ucsb-biomimetic/ising-potts-with-SPADs-discrete/VRSPAD-144/code_and_data/results/coloring_ising_parameter_sweep.png

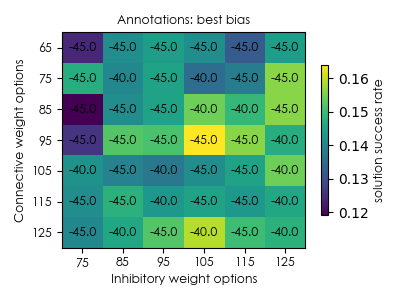
VRSPAD-144/code_and_data/results/coloring_ising_parameter_sweep.png
