ucsb-biomimetic/ising-potts-with-SPADs-discrete/VRSPAD-144/code_and_data/results/coloring_soln_vis.png

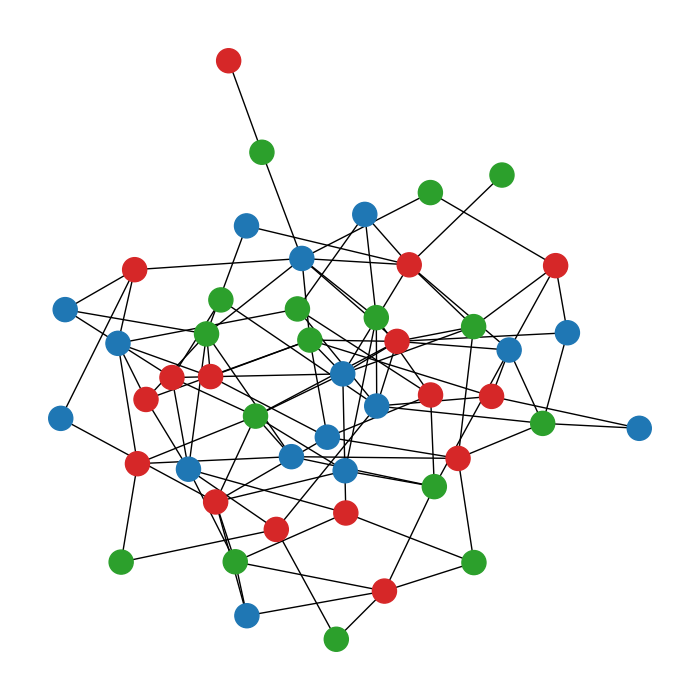
VRSPAD-144/code_and_data/results/coloring_soln_vis.png
