ucsb-biomimetic/ising-potts-with-SPADs-discrete/VRSPAD-144/code_and_data/results/tsp_annealing.png

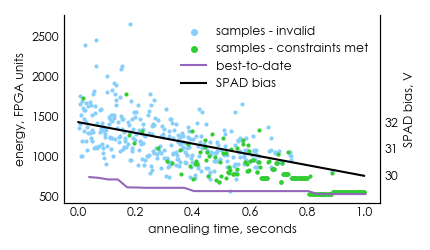
VRSPAD-144/code_and_data/results/tsp_annealing.png
