ucsb-biomimetic/ising-potts-with-SPADs-discrete/VRSPAD-144/pcb_design/VRSPAD-144.kicad_sch

## KiCad design VRSPAD-144/pcb_design/VRSPAD-144.kicad_sch (2023-06-14)

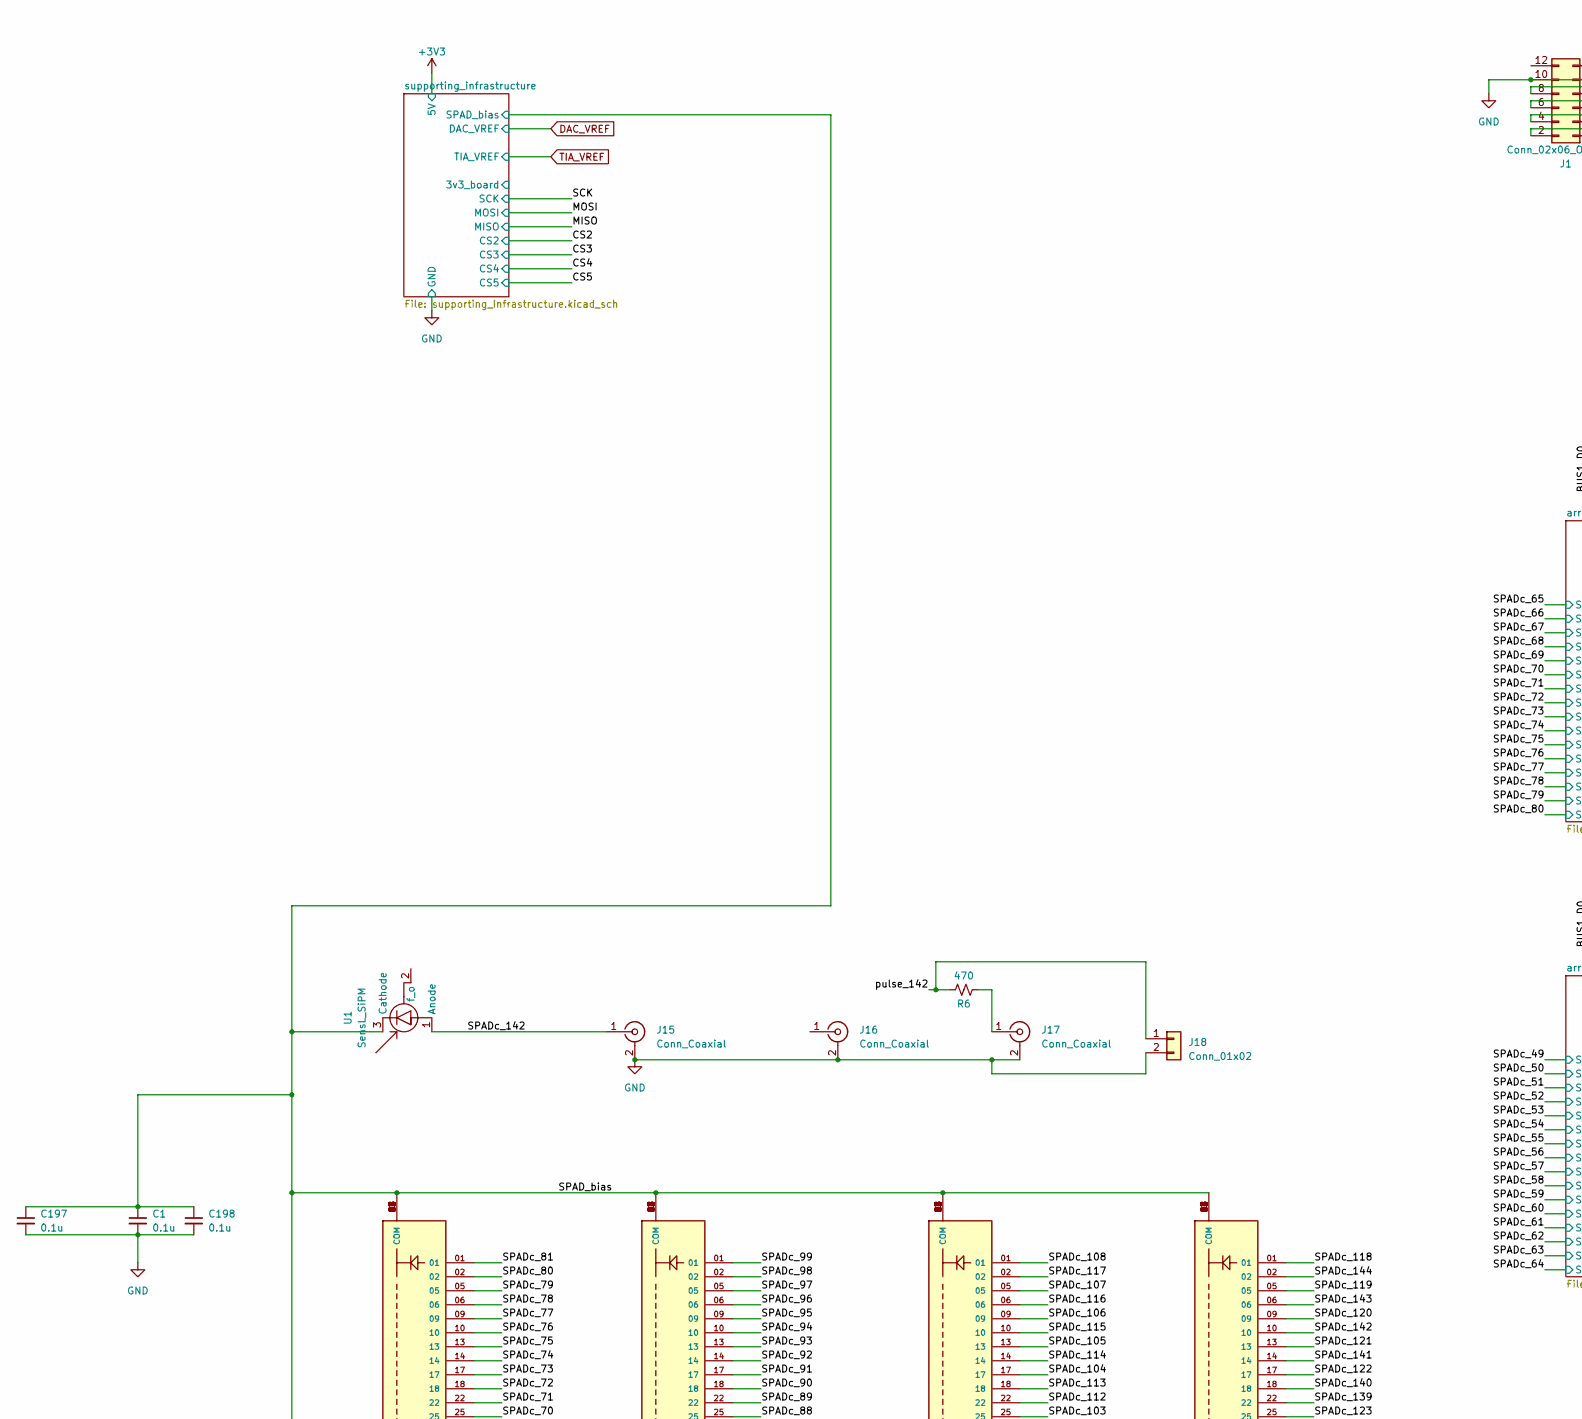
[picture p27: schematic VRSPAD-144.kicad_sch, part in row 1, column 1]

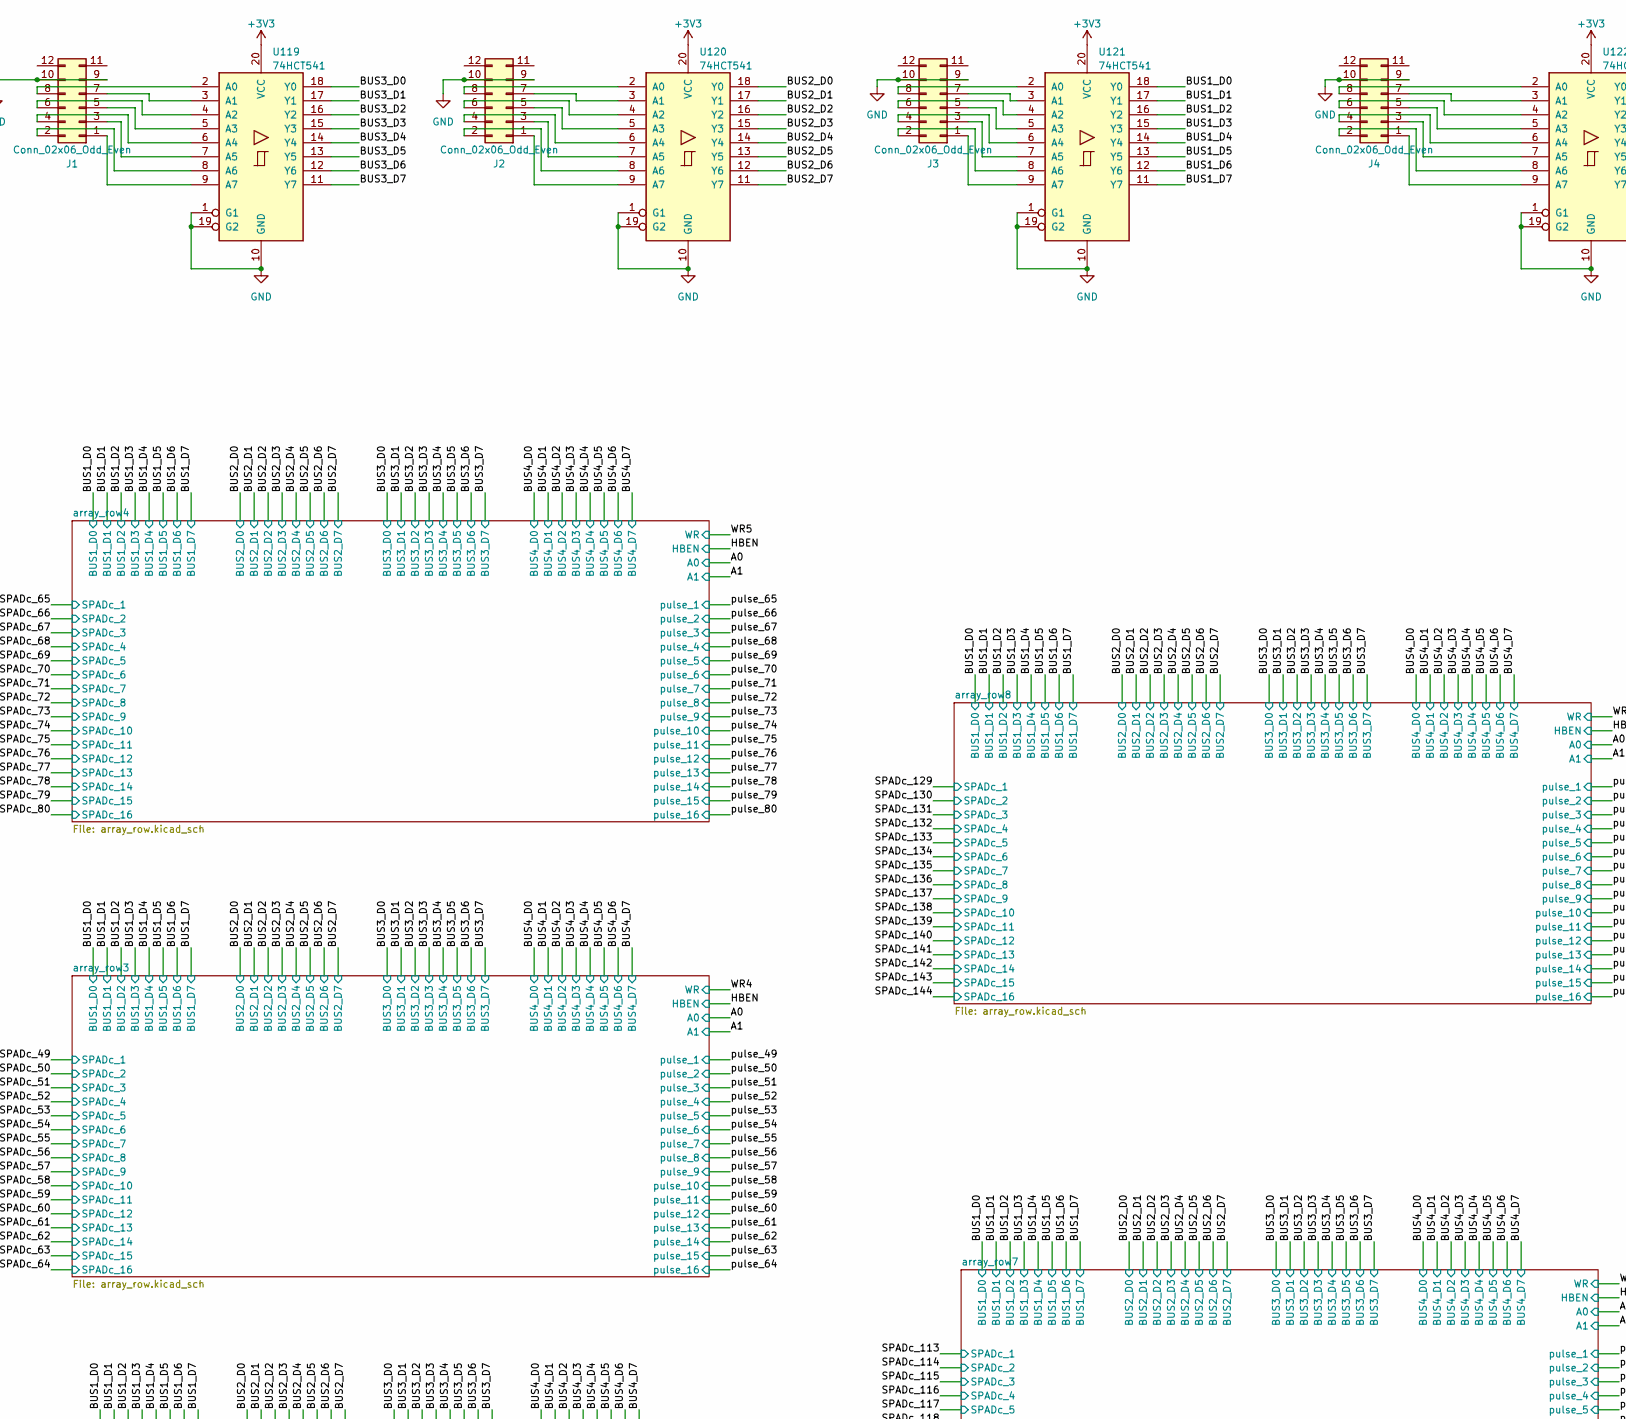
[picture p28: schematic VRSPAD-144.kicad_sch, part in row 1, column 2]

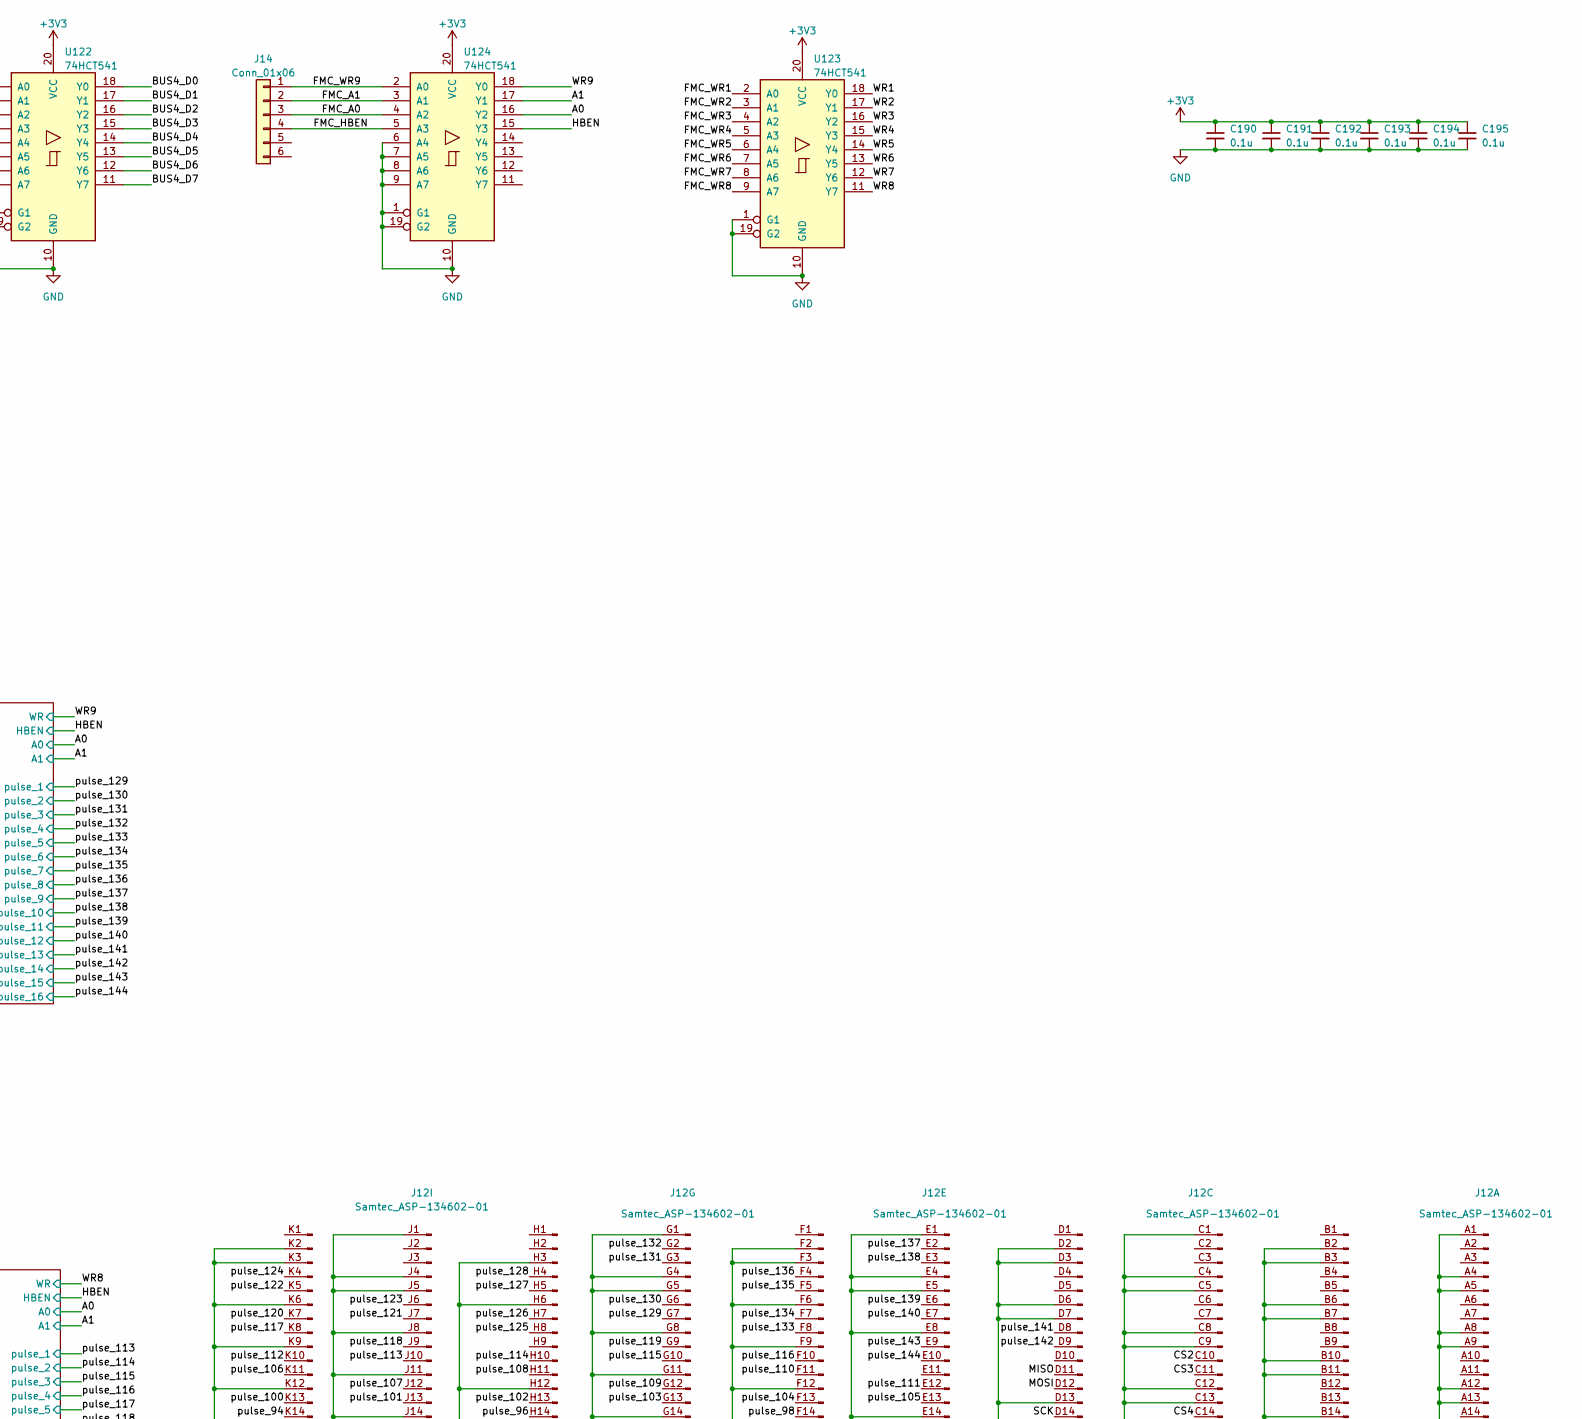
[picture p29: schematic VRSPAD-144.kicad_sch, part in row 1, column 3]

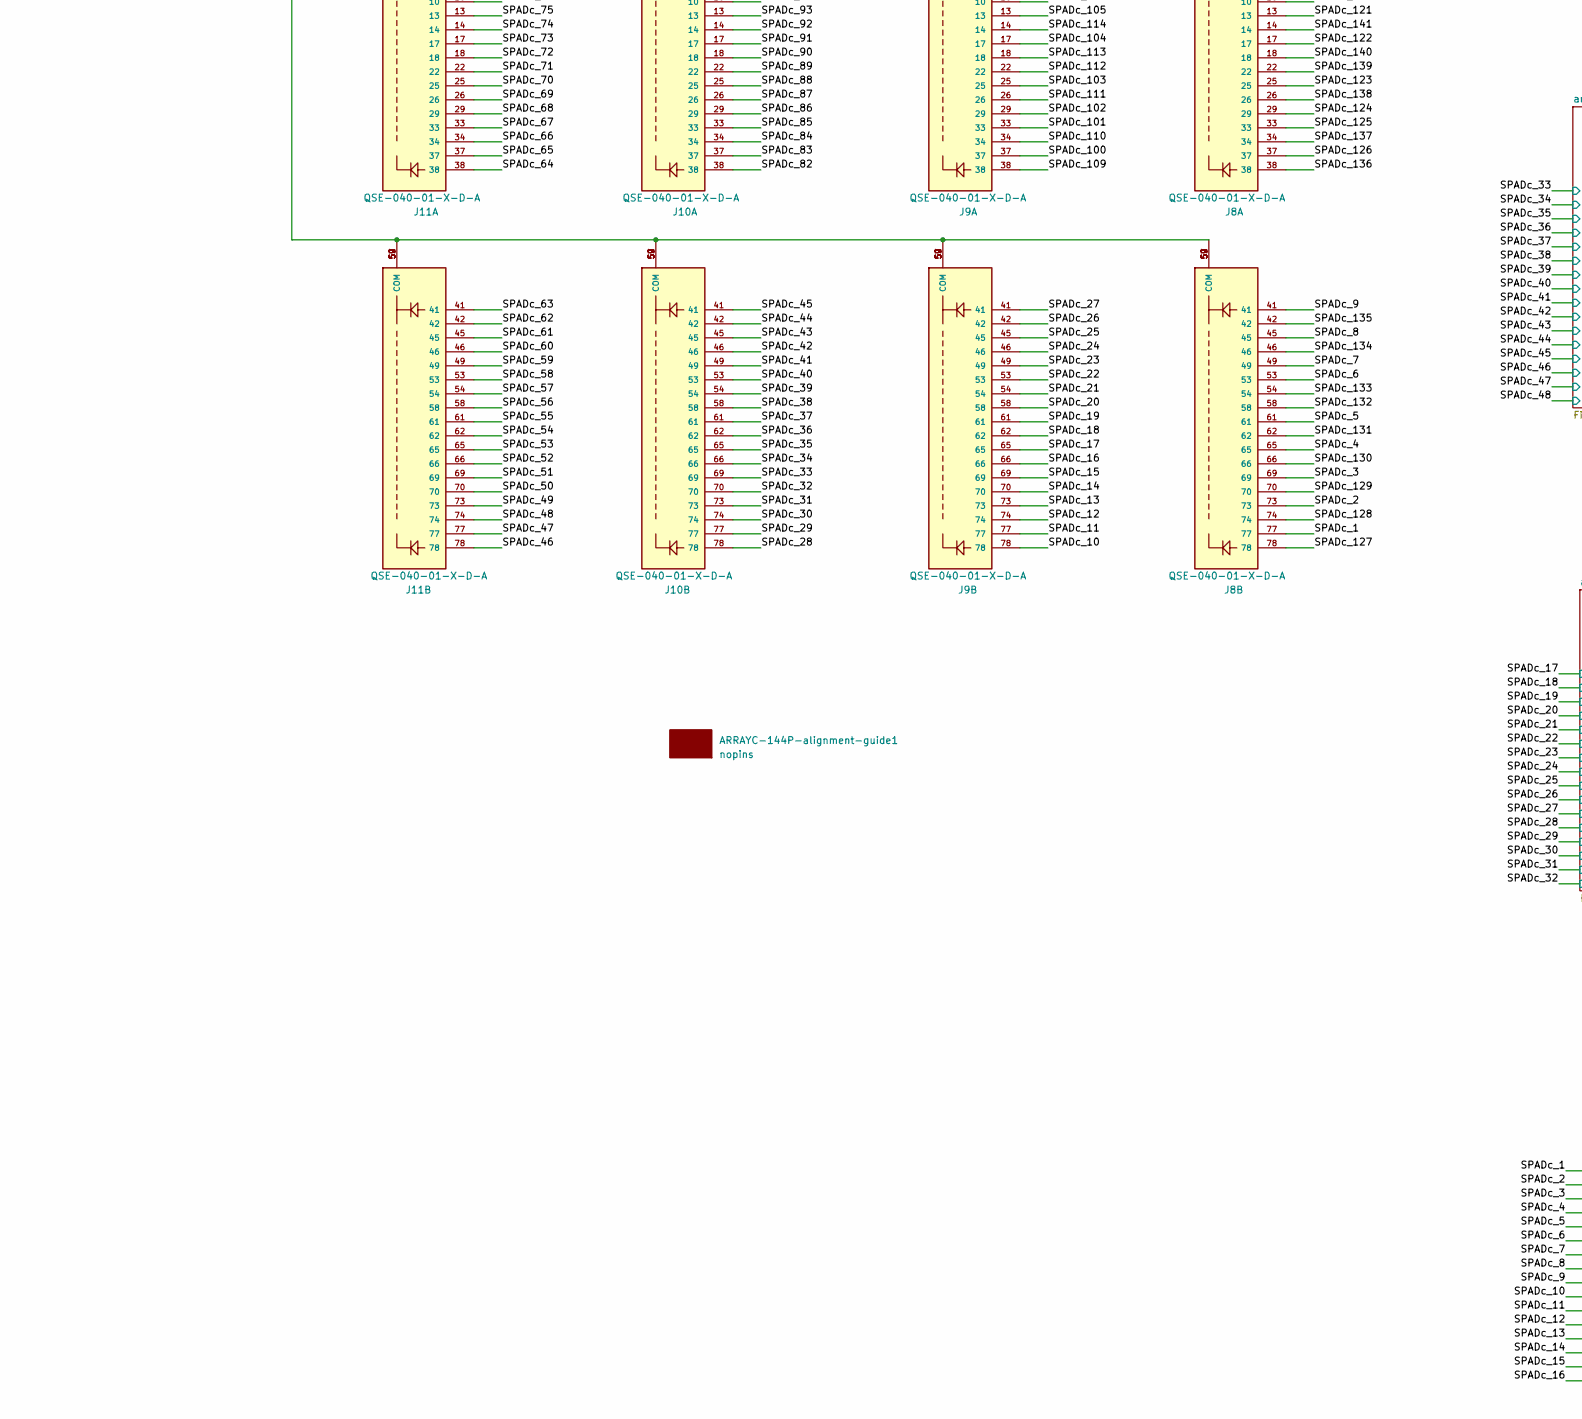
[picture p30: schematic VRSPAD-144.kicad_sch, part in row 2, column 1]

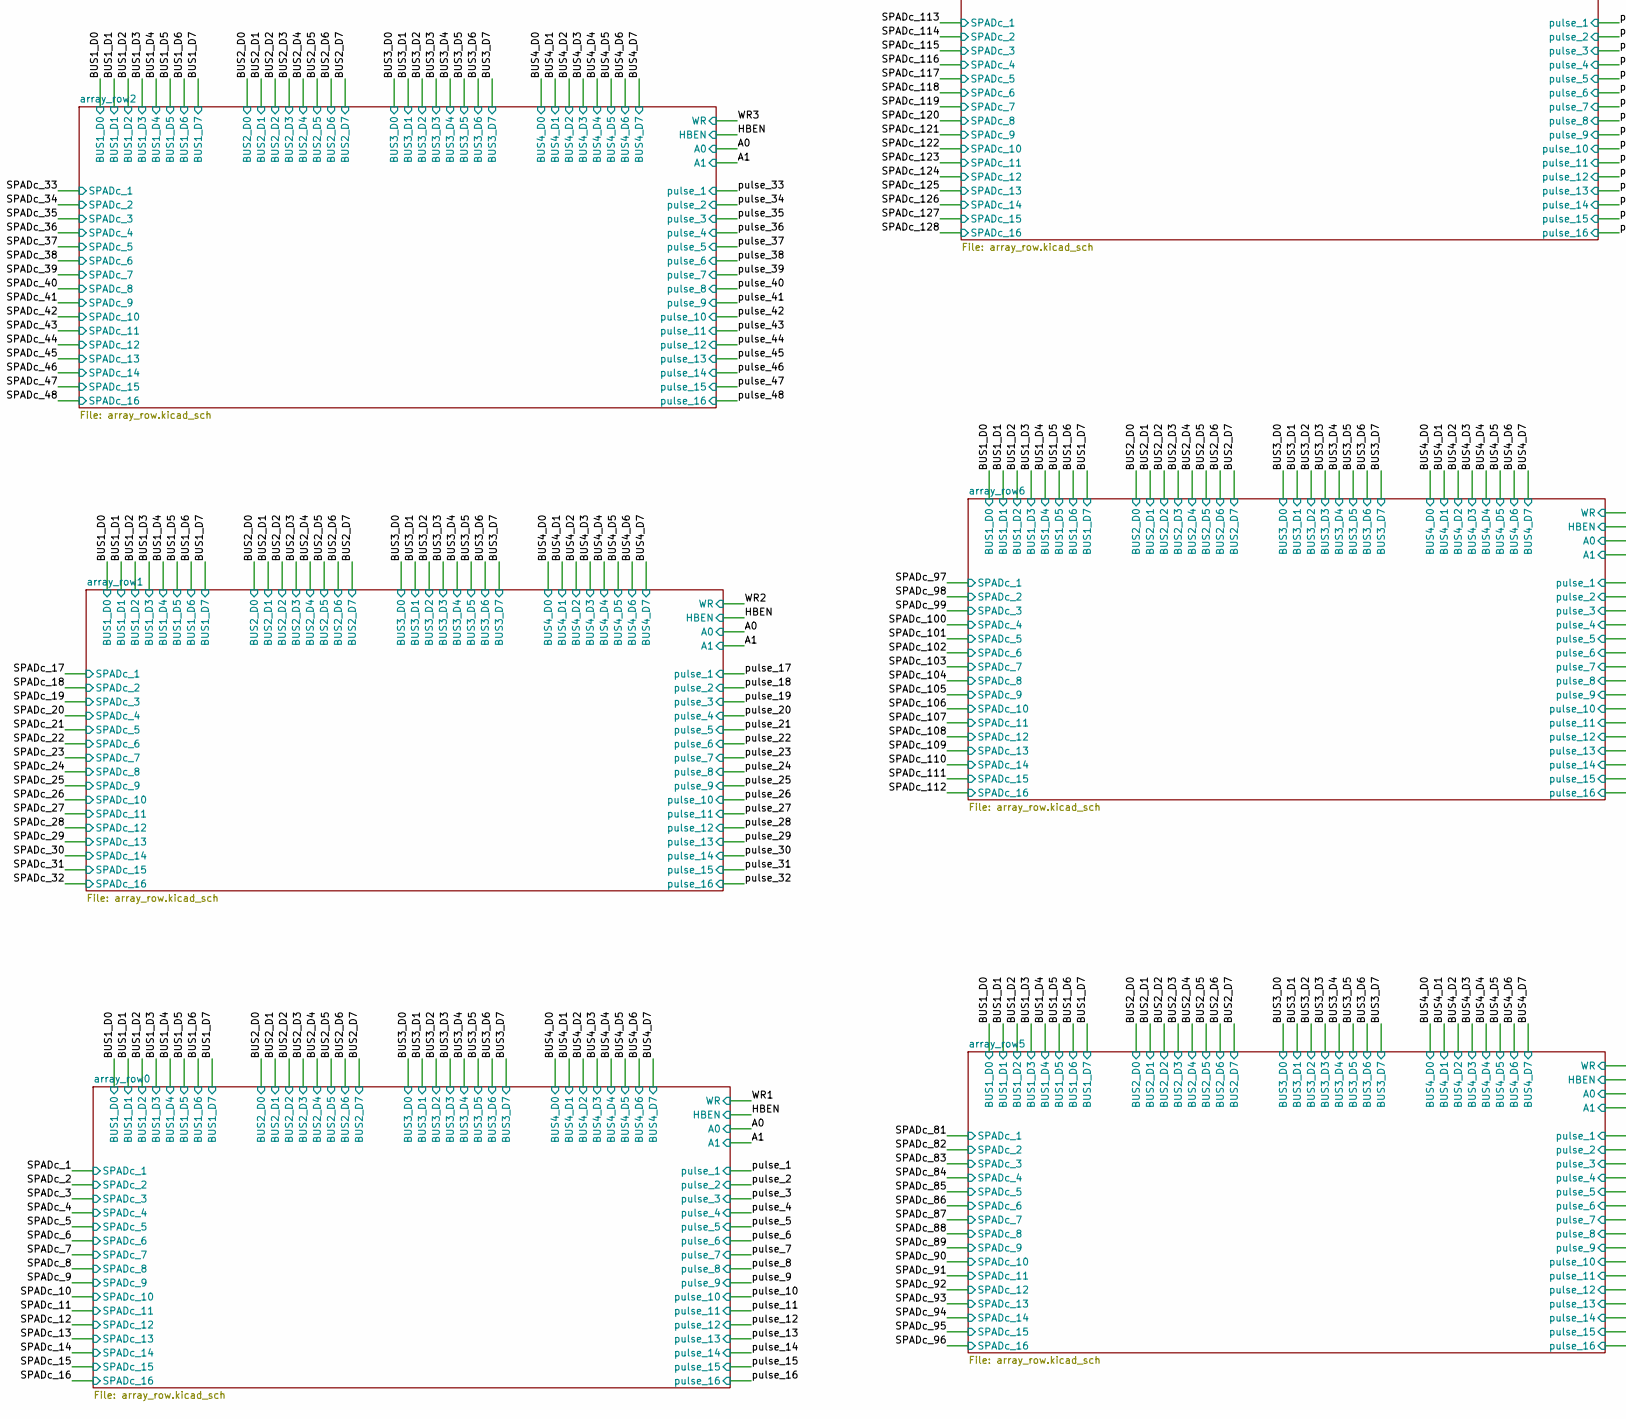
[picture p31: schematic VRSPAD-144.kicad_sch, part in row 2, column 2]

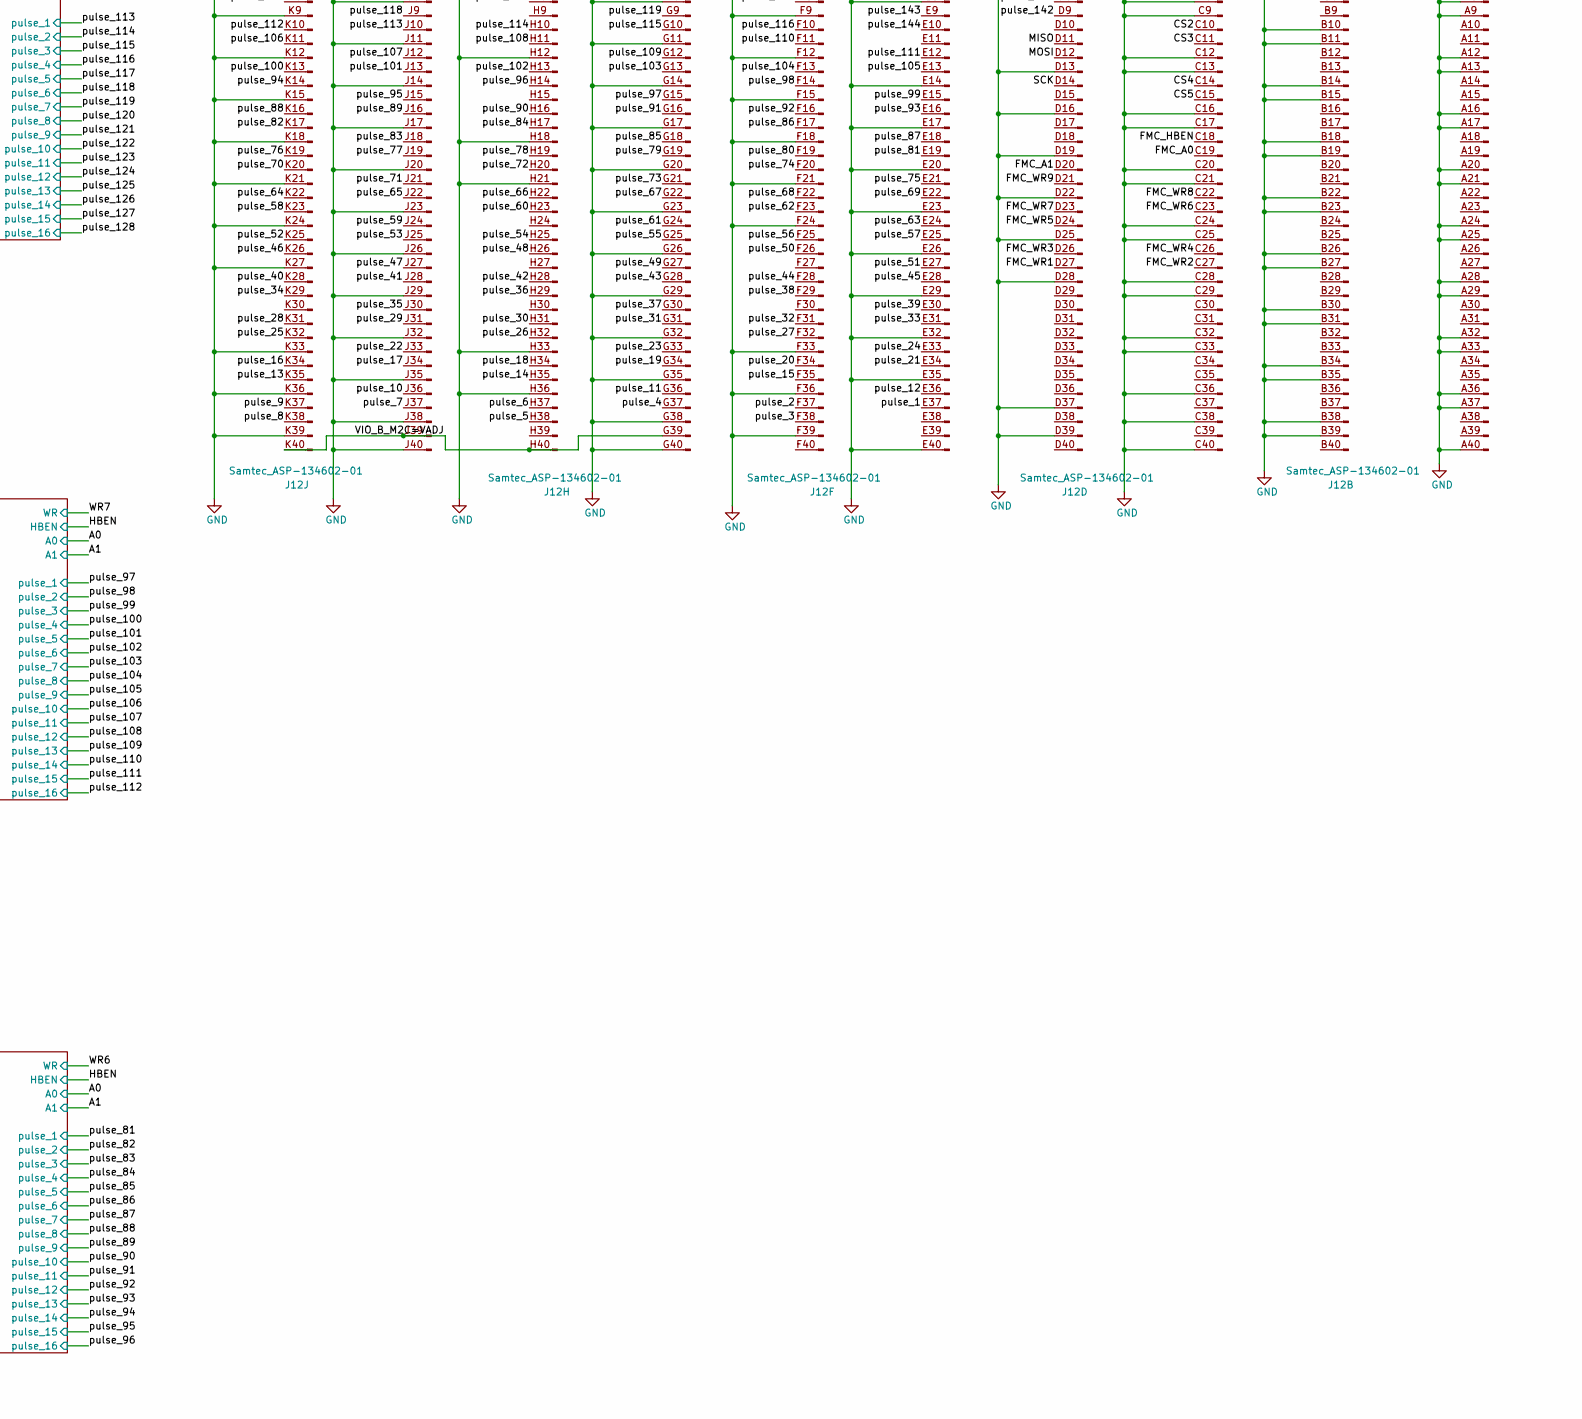
[picture p32: schematic VRSPAD-144.kicad_sch, part in row 2, column 3]

Parts:
ARRAYC-144P-alignment-guide1: nopins; ARRAYC-144P-alignment_guide
C1, C190, C191, C192, C193, C194, C195, C197, C198: 0.1u; C_0603_1608Metric
J1, J2, J3, J4: Conn_02x06_Odd_Even; PinHeader_2x06_P2.54mm_Horizontal
J8, J9, J10, J11: QSE-040-01-X-D-A; SAMTEC_QSE-040-01-X-D-A; PARTREV N
J12: Samtec_ASP-134602-01; Samtec_FMC_ASP-134602-01_10x40_P1.27mm_Vertical
J14: Conn_01x06; PinHeader_1x06_P2.54mm_Vertical
J15, J16, J17: Conn_Coaxial; SMA_Amphenol_132134-16_Vertical
J18: Conn_01x02; PinHeader_1x02_P2.54mm_Vertical
R6: 470; R_0603_1608Metric_Pad0.98x0.95mm_HandSolder
U1: SensL_SiPM; SensL_SiPM_3mm
U119, U120, U121, U122, U123, U124: 74HCT541; TSSOP-20_4.4x6.5mm_P0.65mm

Connections:
+3V3: C190.1, C191.1, C192.1, C193.1, C194.1, C195.1, U119.20 (VCC), U120.20 (VCC), U121.20 (VCC), U122.20 (VCC), U123.20 (VCC), U124.20 (VCC)
A0: U124.16 (Y2)
A1: U124.17 (Y1)
BUS1_D0: U121.18 (Y0)
BUS1_D1: U121.17 (Y1)
BUS1_D2: U121.16 (Y2)
BUS1_D3: U121.15 (Y3)
BUS1_D4: U121.14 (Y4)
BUS1_D5: U121.13 (Y5)
BUS1_D6: U121.12 (Y6)
BUS1_D7: U121.11 (Y7)
BUS2_D0: U120.18 (Y0)
BUS2_D1: U120.17 (Y1)
BUS2_D2: U120.16 (Y2)
BUS2_D3: U120.15 (Y3)
BUS2_D4: U120.14 (Y4)
BUS2_D5: U120.13 (Y5)
BUS2_D6: U120.12 (Y6)
BUS2_D7: U120.11 (Y7)
BUS3_D0: U119.18 (Y0)
BUS3_D1: U119.17 (Y1)
BUS3_D2: U119.16 (Y2)
BUS3_D3: U119.15 (Y3)
BUS3_D4: U119.14 (Y4)
BUS3_D5: U119.13 (Y5)
BUS3_D6: U119.12 (Y6)
BUS3_D7: U119.11 (Y7)
BUS4_D0: U122.18 (Y0)
BUS4_D1: U122.17 (Y1)
BUS4_D2: U122.16 (Y2)
BUS4_D3: U122.15 (Y3)
BUS4_D4: U122.14 (Y4)
BUS4_D5: U122.13 (Y5)
BUS4_D6: U122.12 (Y6)
BUS4_D7: U122.11 (Y7)
CS2: J12.C10 (Pin_10)
CS3: J12.C11 (Pin_11)
CS4: J12.C14 (Pin_14)
CS5: J12.C15 (Pin_15)
FMC_A0: J12.C19 (Pin_19), J14.3, U124.4 (A2)
FMC_A1: J12.D20 (Pin_20), J14.2, U124.3 (A1)
FMC_HBEN: J12.C18 (Pin_18), J14.4, U124.5 (A3)
FMC_WR1: J12.D27 (Pin_27), U123.2 (A0)
FMC_WR2: J12.C27 (Pin_27), U123.3 (A1)
FMC_WR3: J12.D26 (Pin_26), U123.4 (A2)
FMC_WR4: J12.C26 (Pin_26), U123.5 (A3)
FMC_WR5: J12.D24 (Pin_24), U123.6 (A4)
FMC_WR6: J12.C23 (Pin_23), U123.7 (A5)
FMC_WR7: J12.D23 (Pin_23), U123.8 (A6)
FMC_WR8: J12.C22 (Pin_22), U123.9 (A7)
FMC_WR9: J12.D21 (Pin_21), J14.1, U124.2 (A0)
GND: C1.2, C190.2, C191.2, C192.2, C193.2, C194.2, C195.2, C197.2, C198.2, J1.9, J1.10, J2.9, J2.10, J3.9, J3.10, J4.9, J4.10, J12.A1 (Pin_1), J12.A4 (Pin_4), J12.A5 (Pin_5), J12.A8 (Pin_8), J12.A9 (Pin_9), J12.A12 (Pin_12), J12.A13 (Pin_13), J12.A16 (Pin_16), J12.A17 (Pin_17), J12.A20 (Pin_20), J12.A21 (Pin_21), J12.A24 (Pin_24), J12.A25 (Pin_25), J12.A28 (Pin_28), J12.A29 (Pin_29), J12.A32 (Pin_32), J12.A33 (Pin_33), J12.A36 (Pin_36), J12.A37 (Pin_37), J12.A40 (Pin_40), J12.B2 (Pin_2), J12.B3 (Pin_3), J12.B6 (Pin_6), J12.B7 (Pin_7), J12.B10 (Pin_10), J12.B11 (Pin_11), J12.B14 (Pin_14), J12.B15 (Pin_15), J12.B18 (Pin_18), J12.B19 (Pin_19), J12.B22 (Pin_22), J12.B23 (Pin_23), J12.B26 (Pin_26), J12.B27 (Pin_27), J12.B30 (Pin_30), J12.B31 (Pin_31), J12.B34 (Pin_34), J12.B35 (Pin_35), J12.B38 (Pin_38), J12.B39 (Pin_39), J12.C1 (Pin_1), J12.C4 (Pin_4), J12.C5 (Pin_5), J12.C8 (Pin_8), J12.C9 (Pin_9), J12.C12 (Pin_12), J12.C13 (Pin_13), J12.C16 (Pin_16), J12.C17 (Pin_17), J12.C20 (Pin_20), J12.C21 (Pin_21), J12.C24 (Pin_24), J12.C25 (Pin_25), J12.C28 (Pin_28), J12.C29 (Pin_29), J12.C32 (Pin_32), J12.C33 (Pin_33), J12.C36 (Pin_36), J12.C38 (Pin_38), J12.C40 (Pin_40), J12.D2 (Pin_2), J12.D3 (Pin_3), J12.D6 (Pin_6), J12.D7 (Pin_7), J12.D13 (Pin_13), J12.D16 (Pin_16), J12.D19 (Pin_19), J12.D22 (Pin_22), J12.D25 (Pin_25), J12.D28 (Pin_28), J12.D37 (Pin_37), J12.D39 (Pin_39), J12.E1 (Pin_1), J12.E4 (Pin_4), J12.E5 (Pin_5), J12.E8 (Pin_8), J12.E14 (Pin_14), J12.E17 (Pin_17), J12.E20 (Pin_20), J12.E23 (Pin_23), J12.E26 (Pin_26), J12.E29 (Pin_29), J12.E32 (Pin_32), J12.E35 (Pin_35), J12.E40 (Pin_40), J12.F2 (Pin_2), J12.F3 (Pin_3), J12.F6 (Pin_6), J12.F9 (Pin_9), J12.F12 (Pin_12), J12.F15 (Pin_15), J12.F18 (Pin_18), J12.F21 (Pin_21), J12.F24 (Pin_24), J12.F33 (Pin_33), J12.F36 (Pin_36), J12.F39 (Pin_39), J12.G1 (Pin_1), J12.G4 (Pin_4), J12.G5 (Pin_5), J12.G8 (Pin_8), J12.G11 (Pin_11), J12.G14 (Pin_14), J12.G17 (Pin_17), J12.G20 (Pin_20), J12.G23 (Pin_23), J12.G26 (Pin_26), J12.G29 (Pin_29), J12.G32 (Pin_32), J12.G35 (Pin_35), J12.G38 (Pin_38), J12.G40 (Pin_40), J12.H3 (Pin_3), J12.H6 (Pin_6), J12.H12 (Pin_12), J12.H18 (Pin_18), J12.H21 (Pin_21), J12.H33 (Pin_33), J12.H36 (Pin_36), J12.J1 (Pin_1), J12.J4 (Pin_4), J12.J5 (Pin_5), J12.J8 (Pin_8), J12.J11 (Pin_11), J12.J14 (Pin_14), J12.J17 (Pin_17), J12.J20 (Pin_20), J12.J23 (Pin_23), J12.J26 (Pin_26), J12.J29 (Pin_29), J12.J32 (Pin_32), J12.J35 (Pin_35), J12.J38 (Pin_38), J12.J40 (Pin_40), J12.K2 (Pin_2), J12.K3 (Pin_3), J12.K6 (Pin_6), J12.K9 (Pin_9), J12.K12 (Pin_12), J12.K15 (Pin_15), J12.K18 (Pin_18), J12.K21 (Pin_21), J12.K24 (Pin_24), J12.K27 (Pin_27), J12.K33 (Pin_33), J12.K36 (Pin_36), J12.K39 (Pin_39), J15.2 (Ext), J16.2 (Ext), J17.2 (Ext), J18.2, U119.1 (G1), U119.10 (GND), U119.19 (G2), U120.1 (G1), U120.10 (GND), U120.19 (G2), U121.1 (G1), U121.10 (GND), U121.19 (G2), U122.1 (G1), U122.10 (GND), U122.19 (G2), U123.1 (G1), U123.10 (GND), U123.19 (G2), U124.1 (G1), U124.6 (A4), U124.7 (A5), U124.8 (A6), U124.9 (A7), U124.10 (GND), U124.19 (G2)
HBEN: U124.15 (Y3)
MISO: J12.D11 (Pin_11)
MOSI: J12.D12 (Pin_12)
unnamed: J1.1, U119.9 (A7)
unnamed: J1.2, U119.8 (A6)
unnamed: J1.3, U119.7 (A5)
unnamed: J1.4, U119.6 (A4)
unnamed: J1.5, U119.5 (A3)
unnamed: J1.6, U119.4 (A2)
unnamed: J1.7, U119.3 (A1)
unnamed: J1.8, U119.2 (A0)
unnamed: J2.1, U120.9 (A7)
unnamed: J2.2, U120.8 (A6)
unnamed: J2.3, U120.7 (A5)
unnamed: J2.4, U120.6 (A4)
unnamed: J2.5, U120.5 (A3)
unnamed: J2.6, U120.4 (A2)
unnamed: J2.7, U120.3 (A1)
unnamed: J2.8, U120.2 (A0)
unnamed: J3.1, U121.9 (A7)
unnamed: J3.2, U121.8 (A6)
unnamed: J3.3, U121.7 (A5)
unnamed: J3.4, U121.6 (A4)
unnamed: J3.5, U121.5 (A3)
unnamed: J3.6, U121.4 (A2)
unnamed: J3.7, U121.3 (A1)
unnamed: J3.8, U121.2 (A0)
unnamed: J4.1, U122.9 (A7)
unnamed: J4.2, U122.8 (A6)
unnamed: J4.3, U122.7 (A5)
unnamed: J4.4, U122.6 (A4)
unnamed: J4.5, U122.5 (A3)
unnamed: J4.6, U122.4 (A2)
unnamed: J4.7, U122.3 (A1)
unnamed: J4.8, U122.2 (A0)
unnamed: J17.1 (In), R6.1
SCK: J12.D14 (Pin_14)
SPAD_bias: C1.1, C197.1, C198.1, J8.21 (COM), J8.23 (COM), J8.30 (COM), J8.32 (COM), J8.50 (COM), J8.52 (COM), J8.57 (COM), J8.59 (COM), J8.G1 (COM), J8.G2 (COM), J8.G3 (COM), J8.G4 (COM), J8.G5 (COM), J8.G6 (COM), J8.G7 (COM), J8.G8 (COM), J9.21 (COM), J9.23 (COM), J9.30 (COM), J9.32 (COM), J9.50 (COM), J9.52 (COM), J9.57 (COM), J9.59 (COM), J9.G1 (COM), J9.G2 (COM), J9.G3 (COM), J9.G4 (COM), J9.G5 (COM), J9.G6 (COM), J9.G7 (COM), J9.G8 (COM), J10.21 (COM), J10.23 (COM), J10.30 (COM), J10.32 (COM), J10.50 (COM), J10.52 (COM), J10.57 (COM), J10.59 (COM), J10.G1 (COM), J10.G2 (COM), J10.G3 (COM), J10.G4 (COM), J10.G5 (COM), J10.G6 (COM), J10.G7 (COM), J10.G8 (COM), J11.21 (COM), J11.23 (COM), J11.30 (COM), J11.32 (COM), J11.50 (COM), J11.52 (COM), J11.57 (COM), J11.59 (COM), J11.G1 (COM), J11.G2 (COM), J11.G3 (COM), J11.G4 (COM), J11.G5 (COM), J11.G6 (COM), J11.G7 (COM), J11.G8 (COM), U1.3 (Cathode)
SPADc_1: J8.77
SPADc_2: J8.73
SPADc_3: J8.69
SPADc_4: J8.65
SPADc_5: J8.61
SPADc_6: J8.53
SPADc_7: J8.49
SPADc_8: J8.45
SPADc_9: J8.41
SPADc_10: J9.78
SPADc_11: J9.77
SPADc_12: J9.74
SPADc_13: J9.73
SPADc_14: J9.70
SPADc_15: J9.69
SPADc_16: J9.66
SPADc_17: J9.65
SPADc_18: J9.62
SPADc_19: J9.61
SPADc_20: J9.58
SPADc_21: J9.54
SPADc_22: J9.53
SPADc_23: J9.49
SPADc_24: J9.46
SPADc_25: J9.45
SPADc_26: J9.42
SPADc_27: J9.41
SPADc_28: J10.78
SPADc_29: J10.77
SPADc_30: J10.74
SPADc_31: J10.73
SPADc_32: J10.70
SPADc_33: J10.69
SPADc_34: J10.66
SPADc_35: J10.65
SPADc_36: J10.62
SPADc_37: J10.61
SPADc_38: J10.58
SPADc_39: J10.54
SPADc_40: J10.53
SPADc_41: J10.49
SPADc_42: J10.46
SPADc_43: J10.45
SPADc_44: J10.42
SPADc_45: J10.41
SPADc_46: J11.78
SPADc_47: J11.77
SPADc_48: J11.74
SPADc_49: J11.73
SPADc_50: J11.70
SPADc_51: J11.69
SPADc_52: J11.66
SPADc_53: J11.65
SPADc_54: J11.62
SPADc_55: J11.61
SPADc_56: J11.58
SPADc_57: J11.54
SPADc_58: J11.53
SPADc_59: J11.49
SPADc_60: J11.46
SPADc_61: J11.45
SPADc_62: J11.42
SPADc_63: J11.41
SPADc_64: J11.38
SPADc_65: J11.37
SPADc_66: J11.34
SPADc_67: J11.33
SPADc_68: J11.29
SPADc_69: J11.26
SPADc_70: J11.25
SPADc_71: J11.22
SPADc_72: J11.18
SPADc_73: J11.17
SPADc_74: J11.14
SPADc_75: J11.13
SPADc_76: J11.10
SPADc_77: J11.09
SPADc_78: J11.06
SPADc_79: J11.05
SPADc_80: J11.02
SPADc_81: J11.01
SPADc_82: J10.38
SPADc_83: J10.37
SPADc_84: J10.34
SPADc_85: J10.33
SPADc_86: J10.29
SPADc_87: J10.26
SPADc_88: J10.25
SPADc_89: J10.22
SPADc_90: J10.18
SPADc_91: J10.17
SPADc_92: J10.14
SPADc_93: J10.13
SPADc_94: J10.10
SPADc_95: J10.09
SPADc_96: J10.06
SPADc_97: J10.05
SPADc_98: J10.02
SPADc_99: J10.01
SPADc_100: J9.37
SPADc_101: J9.33
SPADc_102: J9.29
SPADc_103: J9.25
SPADc_104: J9.17
SPADc_105: J9.13
SPADc_106: J9.09
SPADc_107: J9.05
SPADc_108: J9.01
SPADc_109: J9.38
SPADc_110: J9.34
SPADc_111: J9.26
SPADc_112: J9.22
SPADc_113: J9.18
SPADc_114: J9.14
SPADc_115: J9.10
SPADc_116: J9.06
SPADc_117: J9.02
SPADc_118: J8.01
SPADc_119: J8.05
SPADc_120: J8.09
SPADc_121: J8.13
SPADc_122: J8.17
SPADc_123: J8.25
SPADc_124: J8.29
SPADc_125: J8.33
SPADc_126: J8.37
SPADc_127: J8.78
SPADc_128: J8.74
SPADc_129: J8.70
SPADc_130: J8.66
SPADc_131: J8.62
SPADc_132: J8.58
SPADc_133: J8.54
SPADc_134: J8.46
SPADc_135: J8.42
SPADc_136: J8.38
SPADc_137: J8.34
SPADc_138: J8.26
SPADc_139: J8.22
SPADc_140: J8.18
SPADc_141: J8.14
SPADc_142: J8.10, J15.1 (In), U1.1 (Anode)
SPADc_143: J8.06
SPADc_144: J8.02
VIO_B_M2C=VADJ: J12.G39 (Pin_39), J12.H40 (Pin_40), J12.J39 (Pin_39), J12.K40 (Pin_40)
WR1: U123.18 (Y0)
WR2: U123.17 (Y1)
WR3: U123.16 (Y2)
WR4: U123.15 (Y3)
WR5: U123.14 (Y4)
WR6: U123.13 (Y5)
WR7: U123.12 (Y6)
WR8: U123.11 (Y7)
WR9: U124.18 (Y0)
pulse_1: J12.E37 (Pin_37)
pulse_2: J12.F37 (Pin_37)
pulse_3: J12.F38 (Pin_38)
pulse_4: J12.G37 (Pin_37)
pulse_5: J12.H38 (Pin_38)
pulse_6: J12.H37 (Pin_37)
pulse_7: J12.J37 (Pin_37)
pulse_8: J12.K38 (Pin_38)
pulse_9: J12.K37 (Pin_37)
pulse_10: J12.J36 (Pin_36)
pulse_11: J12.G36 (Pin_36)
pulse_12: J12.E36 (Pin_36)
pulse_13: J12.K35 (Pin_35)
pulse_14: J12.H35 (Pin_35)
pulse_15: J12.F35 (Pin_35)
pulse_16: J12.K34 (Pin_34)
pulse_17: J12.J34 (Pin_34)
pulse_18: J12.H34 (Pin_34)
pulse_19: J12.G34 (Pin_34)
pulse_20: J12.F34 (Pin_34)
pulse_21: J12.E34 (Pin_34)
pulse_22: J12.J33 (Pin_33)
pulse_23: J12.G33 (Pin_33)
pulse_24: J12.E33 (Pin_33)
pulse_25: J12.K32 (Pin_32)
pulse_26: J12.H32 (Pin_32)
pulse_27: J12.F32 (Pin_32)
pulse_28: J12.K31 (Pin_31)
pulse_29: J12.J31 (Pin_31)
pulse_30: J12.H31 (Pin_31)
pulse_31: J12.G31 (Pin_31)
pulse_32: J12.F31 (Pin_31)
pulse_33: J12.E31 (Pin_31)
pulse_34: J12.K29 (Pin_29)
pulse_35: J12.J30 (Pin_30)
pulse_36: J12.H29 (Pin_29)
pulse_37: J12.G30 (Pin_30)
pulse_38: J12.F29 (Pin_29)
pulse_39: J12.E30 (Pin_30)
pulse_40: J12.K28 (Pin_28)
pulse_41: J12.J28 (Pin_28)
pulse_42: J12.H28 (Pin_28)
pulse_43: J12.G28 (Pin_28)
pulse_44: J12.F28 (Pin_28)
pulse_45: J12.E28 (Pin_28)
pulse_46: J12.K26 (Pin_26)
pulse_47: J12.J27 (Pin_27)
pulse_48: J12.H26 (Pin_26)
pulse_49: J12.G27 (Pin_27)
pulse_50: J12.F26 (Pin_26)
pulse_51: J12.E27 (Pin_27)
pulse_52: J12.K25 (Pin_25)
pulse_53: J12.J25 (Pin_25)
pulse_54: J12.H25 (Pin_25)
pulse_55: J12.G25 (Pin_25)
pulse_56: J12.F25 (Pin_25)
pulse_57: J12.E25 (Pin_25)
pulse_58: J12.K23 (Pin_23)
pulse_59: J12.J24 (Pin_24)
pulse_60: J12.H23 (Pin_23)
pulse_61: J12.G24 (Pin_24)
pulse_62: J12.F23 (Pin_23)
pulse_63: J12.E24 (Pin_24)
pulse_64: J12.K22 (Pin_22)
pulse_65: J12.J22 (Pin_22)
pulse_66: J12.H22 (Pin_22)
pulse_67: J12.G22 (Pin_22)
pulse_68: J12.F22 (Pin_22)
pulse_69: J12.E22 (Pin_22)
pulse_70: J12.K20 (Pin_20)
pulse_71: J12.J21 (Pin_21)
pulse_72: J12.H20 (Pin_20)
pulse_73: J12.G21 (Pin_21)
pulse_74: J12.F20 (Pin_20)
pulse_75: J12.E21 (Pin_21)
pulse_76: J12.K19 (Pin_19)
pulse_77: J12.J19 (Pin_19)
pulse_78: J12.H19 (Pin_19)
pulse_79: J12.G19 (Pin_19)
pulse_80: J12.F19 (Pin_19)
pulse_81: J12.E19 (Pin_19)
pulse_82: J12.K17 (Pin_17)
pulse_83: J12.J18 (Pin_18)
pulse_84: J12.H17 (Pin_17)
pulse_85: J12.G18 (Pin_18)
pulse_86: J12.F17 (Pin_17)
pulse_87: J12.E18 (Pin_18)
pulse_88: J12.K16 (Pin_16)
pulse_89: J12.J16 (Pin_16)
pulse_90: J12.H16 (Pin_16)
pulse_91: J12.G16 (Pin_16)
pulse_92: J12.F16 (Pin_16)
pulse_93: J12.E16 (Pin_16)
pulse_94: J12.K14 (Pin_14)
pulse_95: J12.J15 (Pin_15)
pulse_96: J12.H14 (Pin_14)
pulse_97: J12.G15 (Pin_15)
pulse_98: J12.F14 (Pin_14)
pulse_99: J12.E15 (Pin_15)
pulse_100: J12.K13 (Pin_13)
pulse_101: J12.J13 (Pin_13)
pulse_102: J12.H13 (Pin_13)
pulse_103: J12.G13 (Pin_13)
pulse_104: J12.F13 (Pin_13)
pulse_105: J12.E13 (Pin_13)
pulse_106: J12.K11 (Pin_11)
pulse_107: J12.J12 (Pin_12)
pulse_108: J12.H11 (Pin_11)
pulse_109: J12.G12 (Pin_12)
pulse_110: J12.F11 (Pin_11)
pulse_111: J12.E12 (Pin_12)
pulse_112: J12.K10 (Pin_10)
pulse_113: J12.J10 (Pin_10)
pulse_114: J12.H10 (Pin_10)
pulse_115: J12.G10 (Pin_10)
pulse_116: J12.F10 (Pin_10)
pulse_117: J12.K8 (Pin_8)
pulse_118: J12.J9 (Pin_9)
pulse_119: J12.G9 (Pin_9)
pulse_120: J12.K7 (Pin_7)
pulse_121: J12.J7 (Pin_7)
pulse_122: J12.K5 (Pin_5)
pulse_123: J12.J6 (Pin_6)
pulse_124: J12.K4 (Pin_4)
pulse_125: J12.H8 (Pin_8)
pulse_126: J12.H7 (Pin_7)
pulse_127: J12.H5 (Pin_5)
pulse_128: J12.H4 (Pin_4)
pulse_129: J12.G7 (Pin_7)
pulse_130: J12.G6 (Pin_6)
pulse_131: J12.G3 (Pin_3)
pulse_132: J12.G2 (Pin_2)
pulse_133: J12.F8 (Pin_8)
pulse_134: J12.F7 (Pin_7)
pulse_135: J12.F5 (Pin_5)
pulse_136: J12.F4 (Pin_4)
pulse_137: J12.E2 (Pin_2)
pulse_138: J12.E3 (Pin_3)
pulse_139: J12.E6 (Pin_6)
pulse_140: J12.E7 (Pin_7)
pulse_141: J12.D8 (Pin_8)
pulse_142: J12.D9 (Pin_9), J18.1, R6.2
pulse_143: J12.E9 (Pin_9)
pulse_144: J12.E10 (Pin_10)
