ucsb-biomimetic/ising-potts-with-SPADs-discrete/VRSPAD-144/pcb_design/array-matched-highpass-filters.kicad_sch

## KiCad design VRSPAD-144/pcb_design/array-matched-highpass-filters.kicad_sch (2023-06-14)

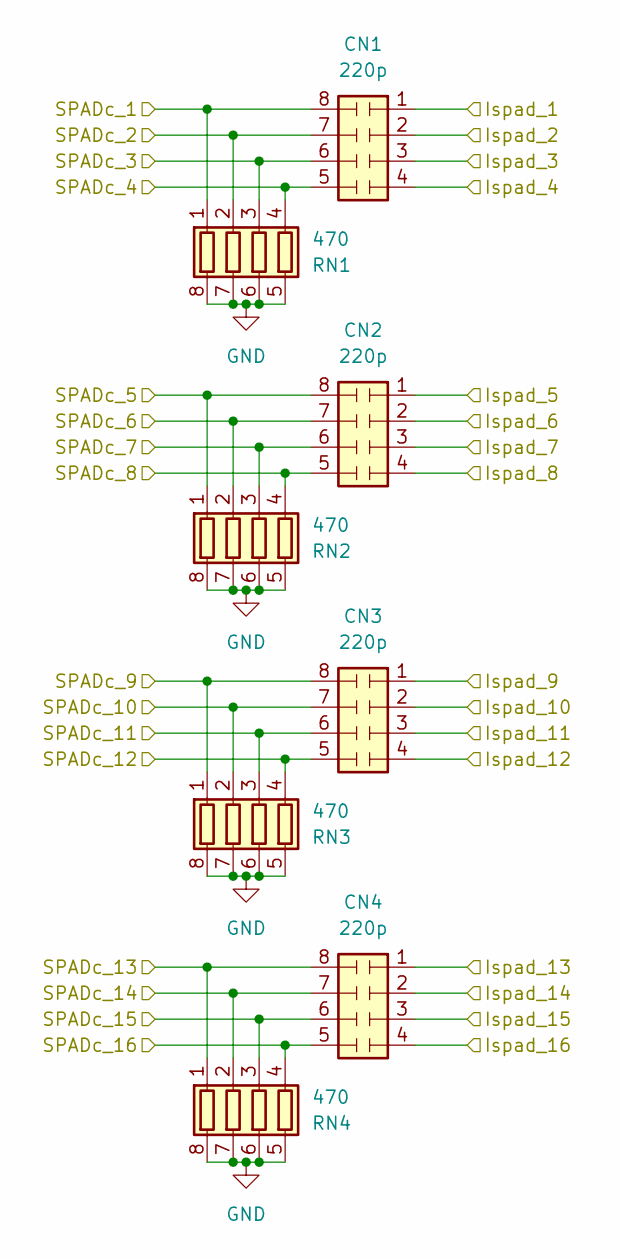
[picture p33: schematic array-matched-highpass-filters.kicad_sch]

Parts:
CN1, CN2, CN3, CN4: 220p; R_Array_Concave_4x0402
RN1, RN2, RN3, RN4: 470; R_Array_Concave_4x0402

Connections:
GND: RN1.5 (R4.2), RN1.6 (R3.2), RN1.7 (R2.2), RN1.8 (R1.2), RN2.5 (R4.2), RN2.6 (R3.2), RN2.7 (R2.2), RN2.8 (R1.2), RN3.5 (R4.2), RN3.6 (R3.2), RN3.7 (R2.2), RN3.8 (R1.2), RN4.5 (R4.2), RN4.6 (R3.2), RN4.7 (R2.2), RN4.8 (R1.2)
Ispad_1: CN1.1 (R1.1)
Ispad_2: CN1.2 (R2.1)
Ispad_3: CN1.3 (R3.1)
Ispad_4: CN1.4 (R4.1)
Ispad_5: CN2.1 (R1.1)
Ispad_6: CN2.2 (R2.1)
Ispad_7: CN2.3 (R3.1)
Ispad_8: CN2.4 (R4.1)
Ispad_9: CN3.1 (R1.1)
Ispad_10: CN3.2 (R2.1)
Ispad_11: CN3.3 (R3.1)
Ispad_12: CN3.4 (R4.1)
Ispad_13: CN4.1 (R1.1)
Ispad_14: CN4.2 (R2.1)
Ispad_15: CN4.3 (R3.1)
Ispad_16: CN4.4 (R4.1)
SPADc_1: CN1.8 (R1.2), RN1.1 (R1.1)
SPADc_2: CN1.7 (R2.2), RN1.2 (R2.1)
SPADc_3: CN1.6 (R3.2), RN1.3 (R3.1)
SPADc_4: CN1.5 (R4.2), RN1.4 (R4.1)
SPADc_5: CN2.8 (R1.2), RN2.1 (R1.1)
SPADc_6: CN2.7 (R2.2), RN2.2 (R2.1)
SPADc_7: CN2.6 (R3.2), RN2.3 (R3.1)
SPADc_8: CN2.5 (R4.2), RN2.4 (R4.1)
SPADc_9: CN3.8 (R1.2), RN3.1 (R1.1)
SPADc_10: CN3.7 (R2.2), RN3.2 (R2.1)
SPADc_11: CN3.6 (R3.2), RN3.3 (R3.1)
SPADc_12: CN3.5 (R4.2), RN3.4 (R4.1)
SPADc_13: CN4.8 (R1.2), RN4.1 (R1.1)
SPADc_14: CN4.7 (R2.2), RN4.2 (R2.1)
SPADc_15: CN4.6 (R3.2), RN4.3 (R3.1)
SPADc_16: CN4.5 (R4.2), RN4.4 (R4.1)
