ucsb-biomimetic/ising-potts-with-SPADs-discrete/VRSPAD-144/pcb_design/quad_channel.kicad_sch

## KiCad design VRSPAD-144/pcb_design/quad_channel.kicad_sch (2023-06-14)

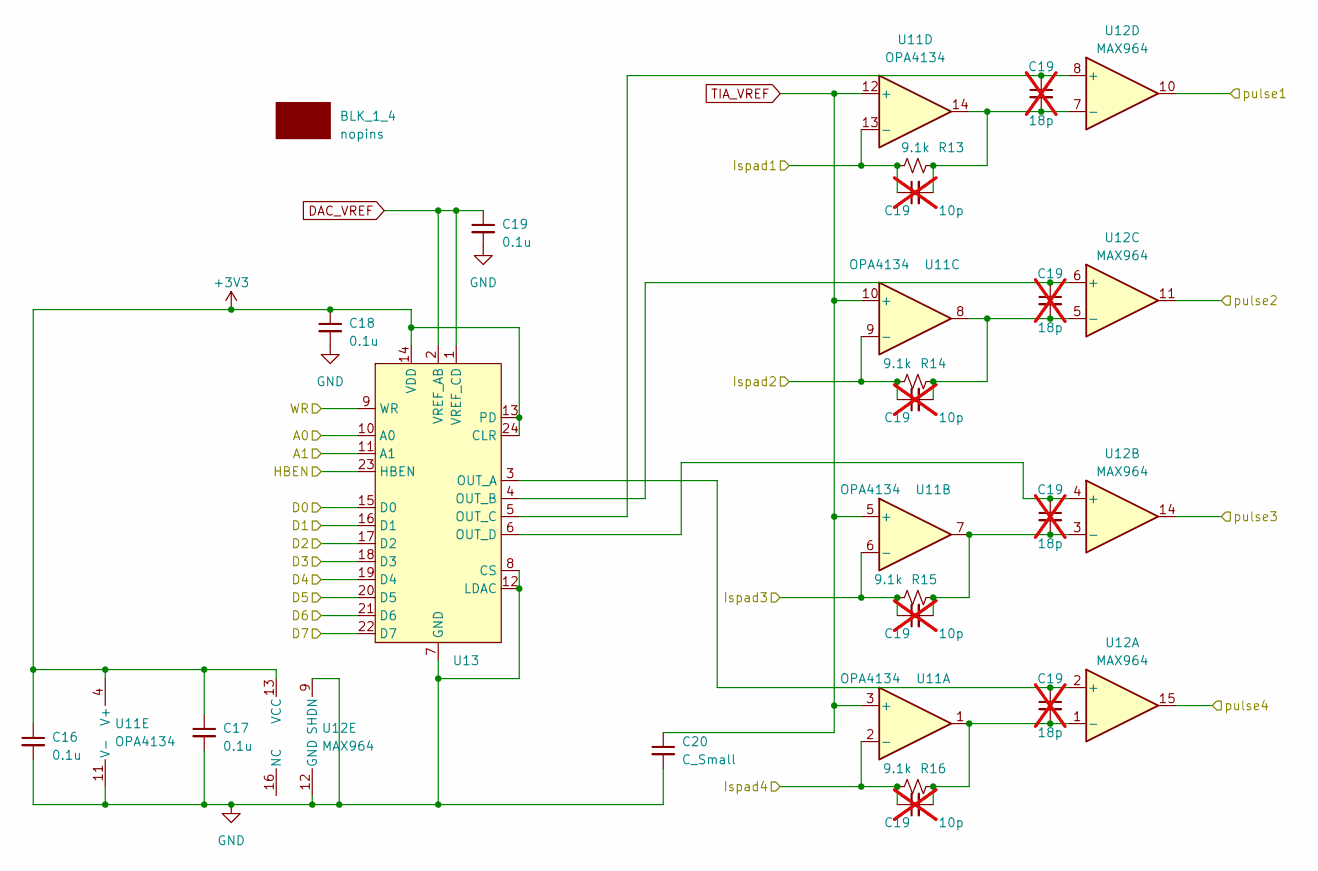
[picture p34: schematic quad_channel.kicad_sch]

Parts:
BLK_1_4: nopins; routing_guide_16T
C16, C17, C18: 0.1u; C_0402_1005Metric
C19: 18p; C_0402_1005Metric; not fitted
C20: C_Small; C_0402_1005Metric
R13, R14, R15, R16: 9.1k; R_0402_1005Metric
U11: OPA4134; TSSOP-14_4.4x5mm_P0.65mm
U12: MAX964; QSOP-16_3.9x4.9mm_P0.635mm
U13: TSSOP-24_4.4x7.8mm_P0.65mm

Connections:
+3V3: C16.1, C17.1, C18.1, U11.4 (V+), U12.13 (VCC), U13.13 (PD), U13.14 (VDD), U13.24 (CLR)
A0: U13.10 (A0)
A1: U13.11 (A1)
D0: U13.15 (D0)
D1: U13.16 (D1)
D2: U13.17 (D2)
D3: U13.18 (D3)
D4: U13.19 (D4)
D5: U13.20 (D5)
D6: U13.21 (D6)
D7: U13.22 (D7)
DAC_VREF: C19.1, U13.1 (VREF_CD), U13.2 (VREF_AB)
GND: C16.2, C17.2, C18.2, C19.2, C20.2, U11.11 (V-), U12.9 (SHDN), U12.12 (GND), U13.7 (GND), U13.8 (CS), U13.12 (LDAC)
HBEN: U13.23 (HBEN)
Ispad1: C19.1, R13.1, U11.13 (-)
Ispad2: C19.1, R14.1, U11.9 (-)
Ispad3: C19.1, R15.1, U11.6 (-)
Ispad4: C19.1, R16.1, U11.2 (-)
unnamed: C19.1, U12.2 (+), U12.4 (+), U12.6 (+), U12.8 (+), U13.3 (OUT_A), U13.4 (OUT_B), U13.5 (OUT_C), U13.6 (OUT_D)
unnamed: C19.2, R13.2, R14.2, R15.2, R16.2, U11.1, U11.7, U11.8, U11.14, U12.1 (-), U12.3 (-), U12.5 (-), U12.7 (-)
TIA_VREF: C20.1, U11.3 (+), U11.5 (+), U11.10 (+), U11.12 (+)
WR: U13.9 (WR)
pulse1: U12.10
pulse2: U12.11
pulse3: U12.14
pulse4: U12.15
