ucsb-biomimetic/ising-potts-with-SPADs-discrete/VRSPAD-144/pcb_design/supporting_infrastructure.kicad_sch

## KiCad design VRSPAD-144/pcb_design/supporting_infrastructure.kicad_sch (2023-06-14)

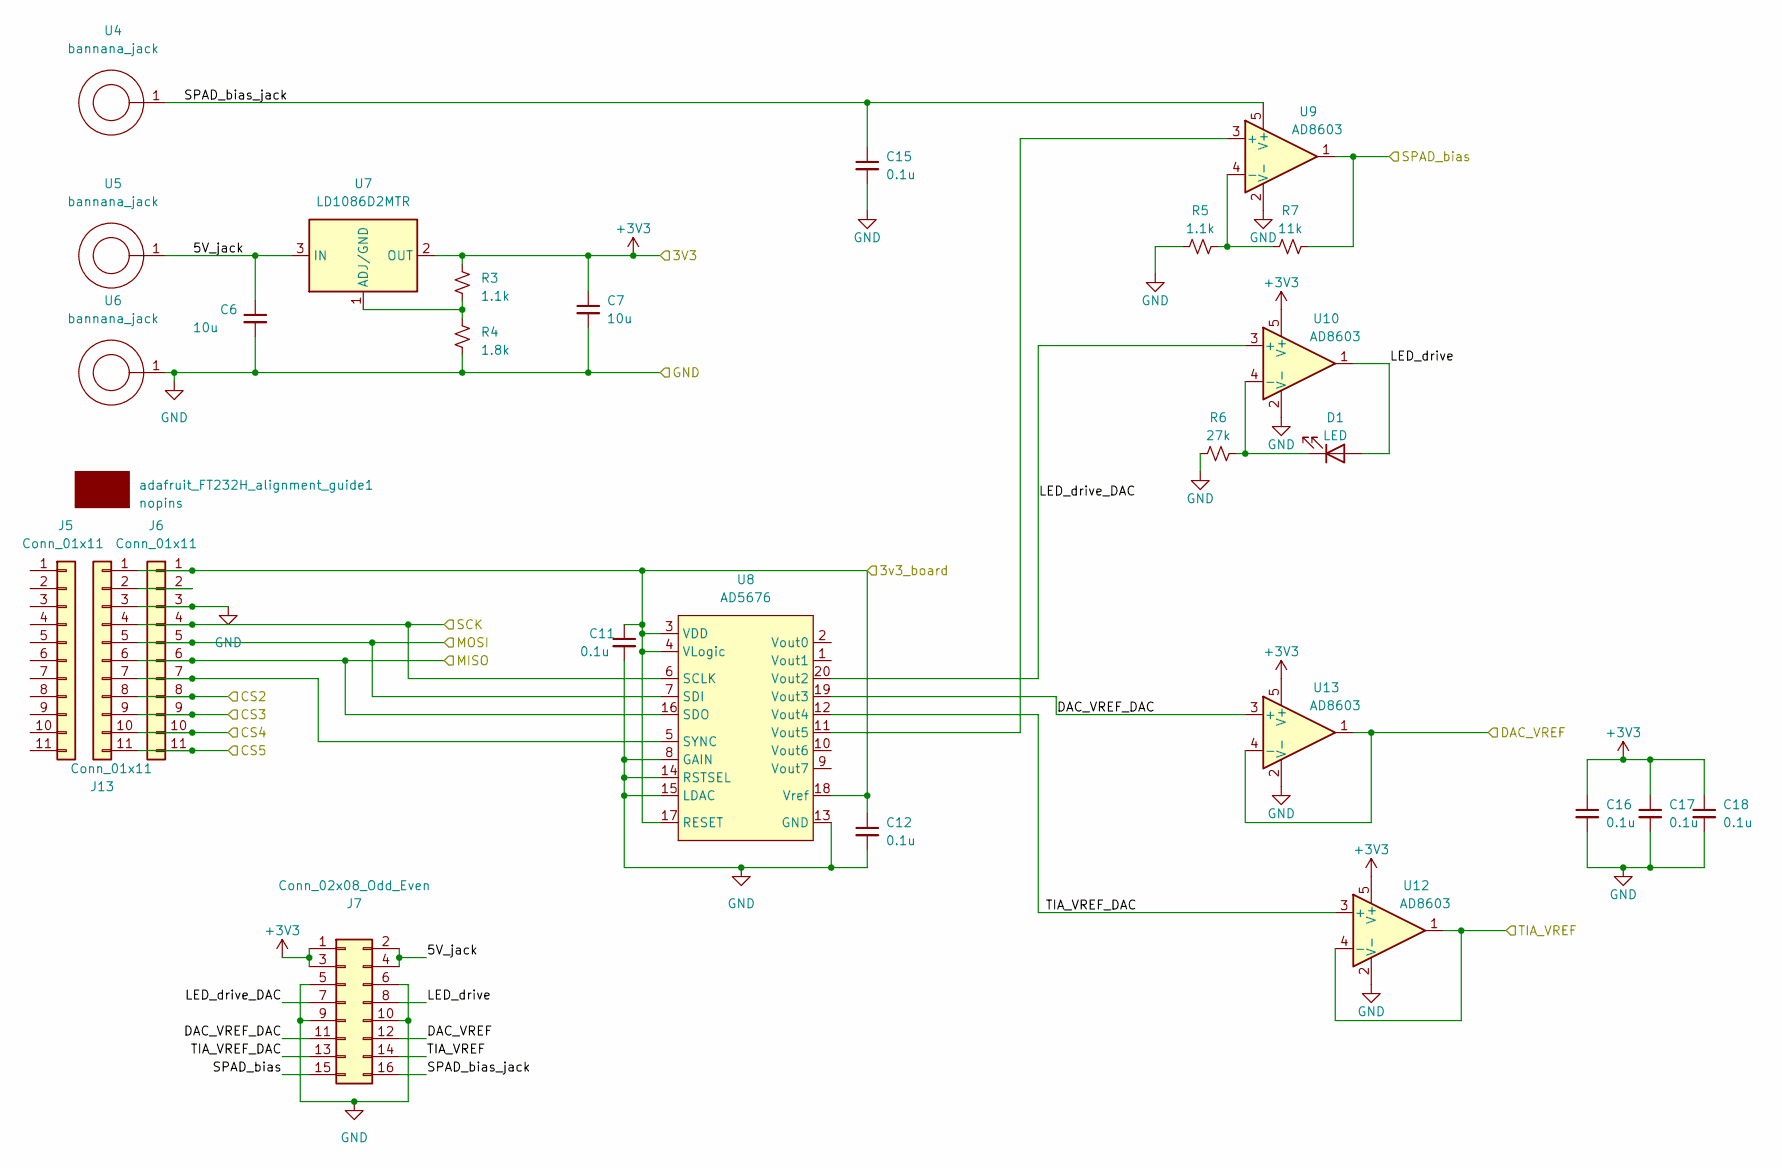
[picture p35: schematic supporting_infrastructure.kicad_sch]

Parts:
C6, C7: 10u; C_0603_1608Metric_Pad1.08x0.95mm_HandSolder
C11, C12, C15, C16, C17, C18: 0.1u; C_0603_1608Metric_Pad1.08x0.95mm_HandSolder
D1: LED; LED_D5.0mm
J5, J6, J13: Conn_01x11; PinHeader_1x11_P2.54mm_Vertical
J7: Conn_02x08_Odd_Even; PinHeader_2x08_P2.54mm_Vertical
R3, R5: 1.1k; R_0603_1608Metric_Pad0.98x0.95mm_HandSolder
R4: 1.8k; R_0603_1608Metric_Pad0.98x0.95mm_HandSolder
R6: 27k; R_0603_1608Metric_Pad0.98x0.95mm_HandSolder
R7: 11k; R_0603_1608Metric_Pad0.98x0.95mm_HandSolder
U4, U5, U6: bannana_jack; CT3151-Horizontal
U7: LD1086D2MTR; TO-263-3_TabPin2
U8: AD5676; TSSOP-20_4.4x6.5mm_P0.65mm
U9, U10, U12, U13: AD8603; TSOT-23-5
adafruit_FT232H_alignment_guide1: nopins; adafruit_FT232H_alignment_guide

Connections:
3v3_board: C11.1, C12.1, J6.1, J13.1, U8.3 (VDD), U8.4 (VLogic), U8.17 (RESET), U8.18 (Vref)
5V_jack: C6.1, J7.2, J7.4, U5.1, U7.3 (IN)
+3V3: C7.1, C16.1, C17.1, C18.1, J7.1, J7.3, R3.1, U7.2 (OUT), U10.5 (V+), U12.5 (V+), U13.5 (V+)
CS2: J6.8, J13.8
CS3: J6.9, J13.9
CS4: J6.10, J13.10
CS5: J6.11, J13.11
DAC_VREF: J7.12, U13.1, U13.4 (-)
DAC_VREF_DAC: J7.11, U8.19 (Vout3), U13.3 (+)
GND: C6.2, C7.2, C11.2, C12.2, C15.2, C16.2, C17.2, C18.2, J6.3, J7.5, J7.6, J7.9, J7.10, J13.3, R4.2, R5.2, R6.2, U6.1, U8.8 (GAIN), U8.13 (GND), U8.14 (RSTSEL), U8.15 (LDAC), U9.2 (V-), U10.2 (V-), U12.2 (V-), U13.2 (V-)
LED_drive: D1.2 (A), J7.8, U10.1
LED_drive_DAC: J7.7, U8.20 (Vout2), U10.3 (+)
MISO: J6.6, J13.6, U8.16 (SDO)
MOSI: J6.5, J13.5, U8.7 (SDI)
unnamed: D1.1 (K), R6.1, U10.4 (-)
unnamed: J6.2, J13.2
unnamed: J6.7, J13.7, U8.5 (SYNC)
unnamed: R3.2, R4.1, U7.1 (ADJ/GND)
unnamed: R5.1, R7.2, U9.4 (-)
unnamed: U8.11 (Vout5), U9.3 (+)
SCK: J6.4, J13.4, U8.6 (SCLK)
SPAD_bias: J7.15, R7.1, U9.1
SPAD_bias_jack: C15.1, J7.16, U4.1, U9.5 (V+)
TIA_VREF: J7.14, U12.1, U12.4 (-)
TIA_VREF_DAC: J7.13, U8.12 (Vout4), U12.3 (+)
